martan3d/OpenPTC/Transmitter/OpenPTC/message.h

#include <avr/io.h>
#include <avr/interrupt.h>

#if defined(__cplusplus)
extern "C" {
#endif

#ifndef MESSAGE_H_
#define MESSAGE_H_

void processDirectedMessage();

#endif /* MESSAGE_H_ */

#if defined(__cplusplus)
}
#endif
